RoboAG/projekt_gluecksrad/Bilder/Entwicklung/2018_02_17_grobe_Platinenanordnung.jpg

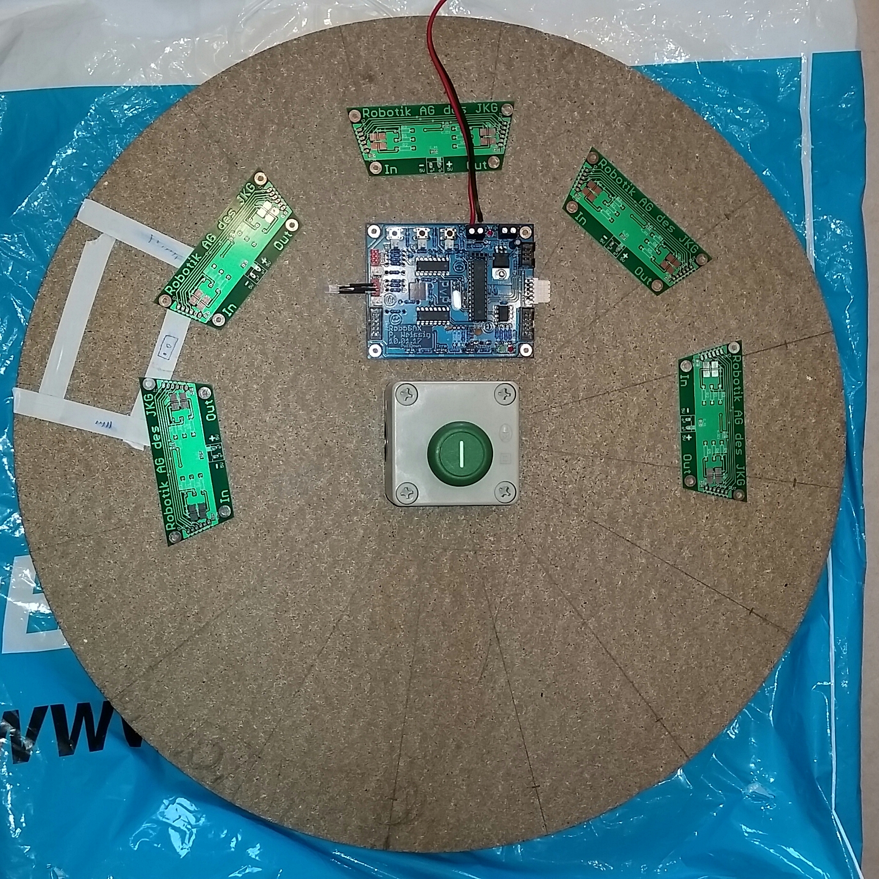
Bilder/Entwicklung/2018_02_17_grobe_Platinenanordnung.jpg
