RoboAG/projekt_gluecksrad/Bilder/Entwicklung/2018_03_07_gluecksrad_zwischenstand.jpg

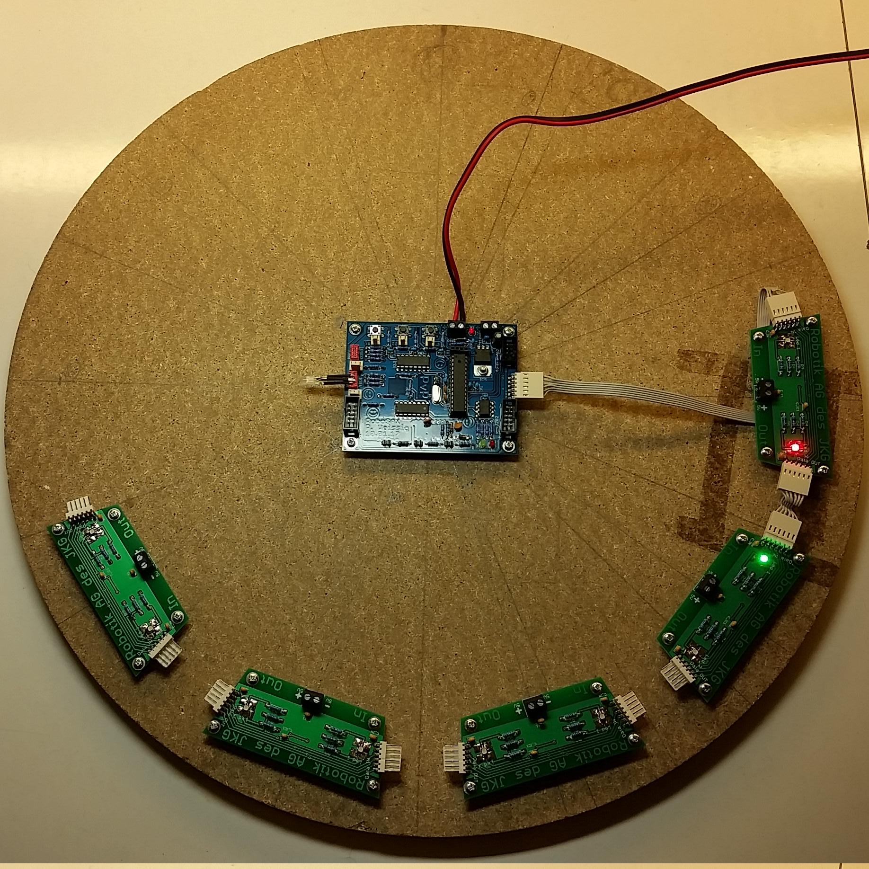
Bilder/Entwicklung/2018_03_07_gluecksrad_zwischenstand.jpg
