RoboAG/projekt_gluecksrad/Bilder/Entwicklung/2018_03_11_stehendes_Stativ.jpg

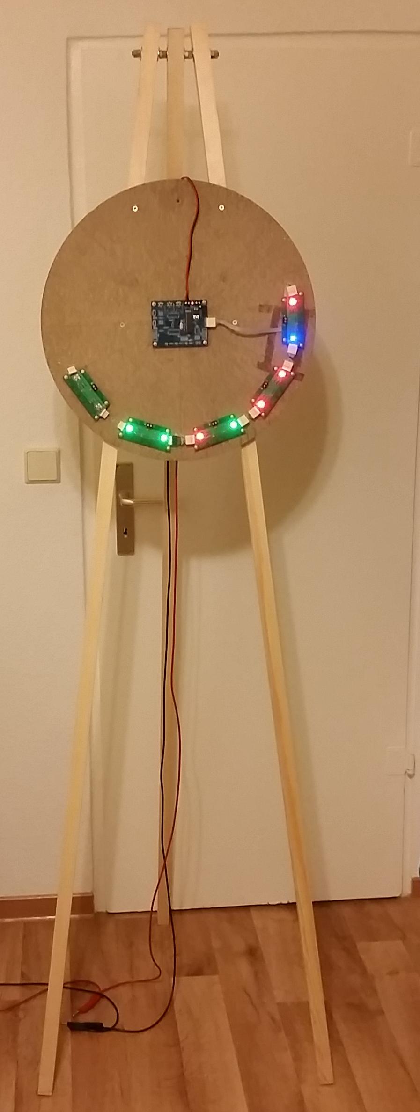
Bilder/Entwicklung/2018_03_11_stehendes_Stativ.jpg
