RoboAG/projekt_gluecksrad/Schaltungen/LED-Platine/2017_06_25_tim/circuit.png

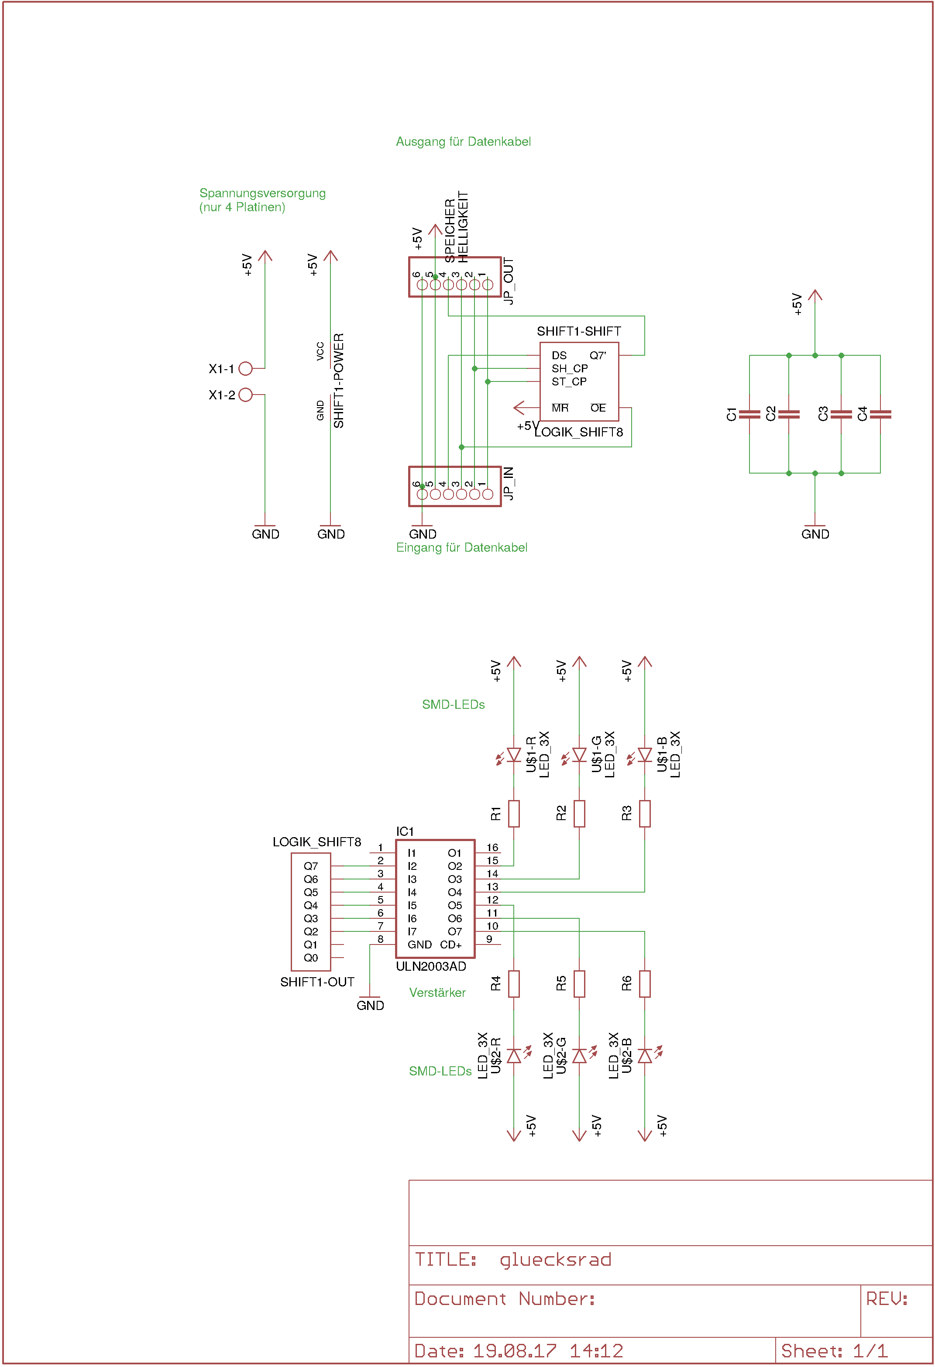
Schaltungen/LED-Platine/2017_06_25_tim/circuit.png
