RoboAG/projekt_gluecksrad/Schaltungen/LED-Platine/2017_06_25_tim/parts_bottom.png

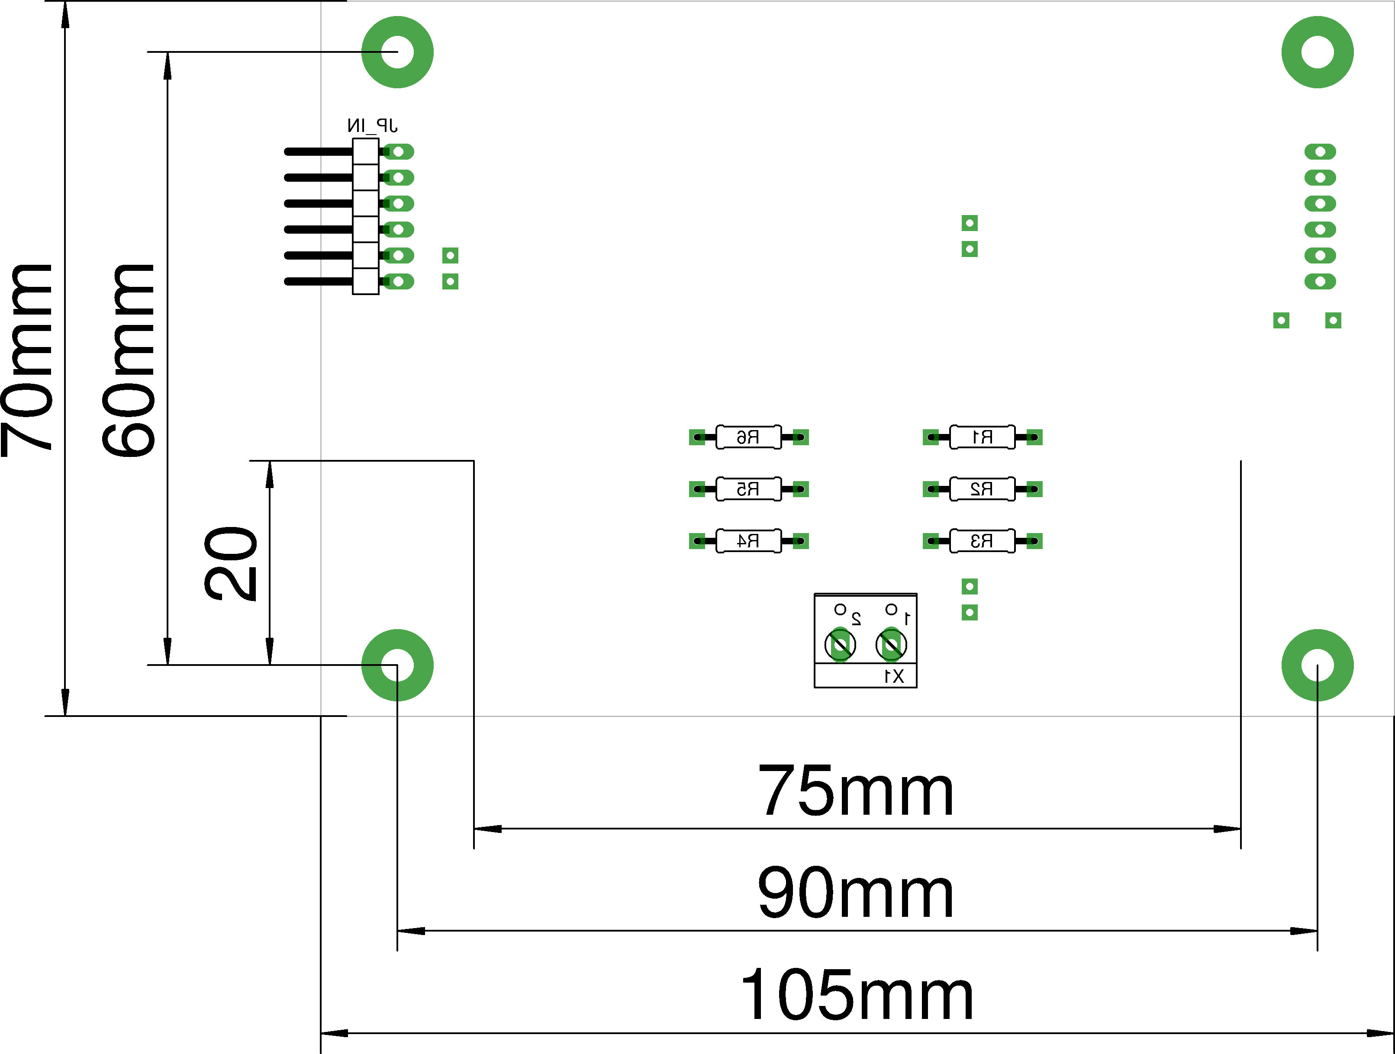
Schaltungen/LED-Platine/2017_06_25_tim/parts_bottom.png
