RoboAG/projekt_gluecksrad/Schaltungen/LED-Platine/2018_01_31_neu/export/images/parts_bottom.png

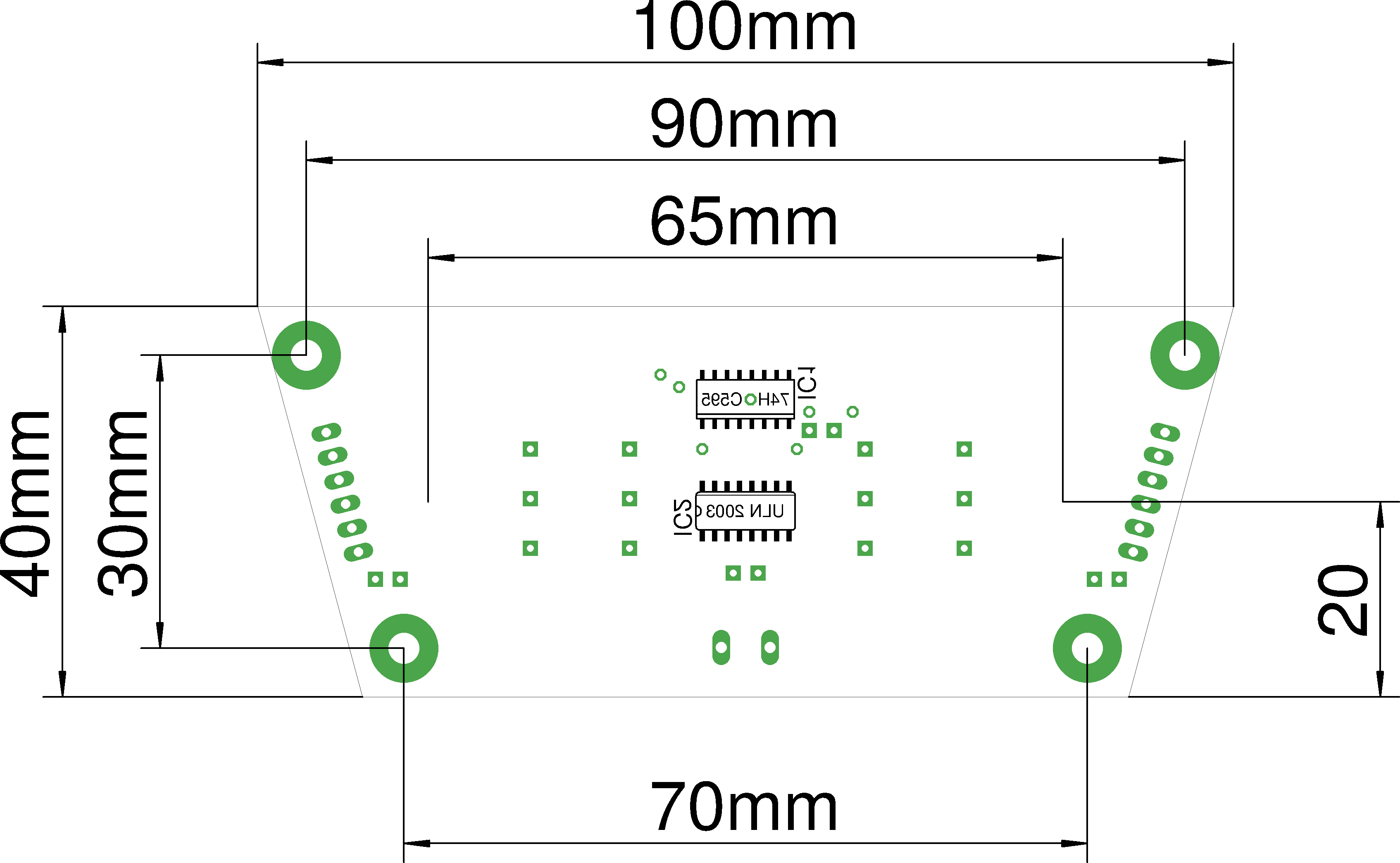
Schaltungen/LED-Platine/2018_01_31_neu/export/images/parts_bottom.png
