RoboAG/projekt_gluecksrad/Schaltungen/LED-Platine/2018_01_31_neu/export/images/parts_top.png

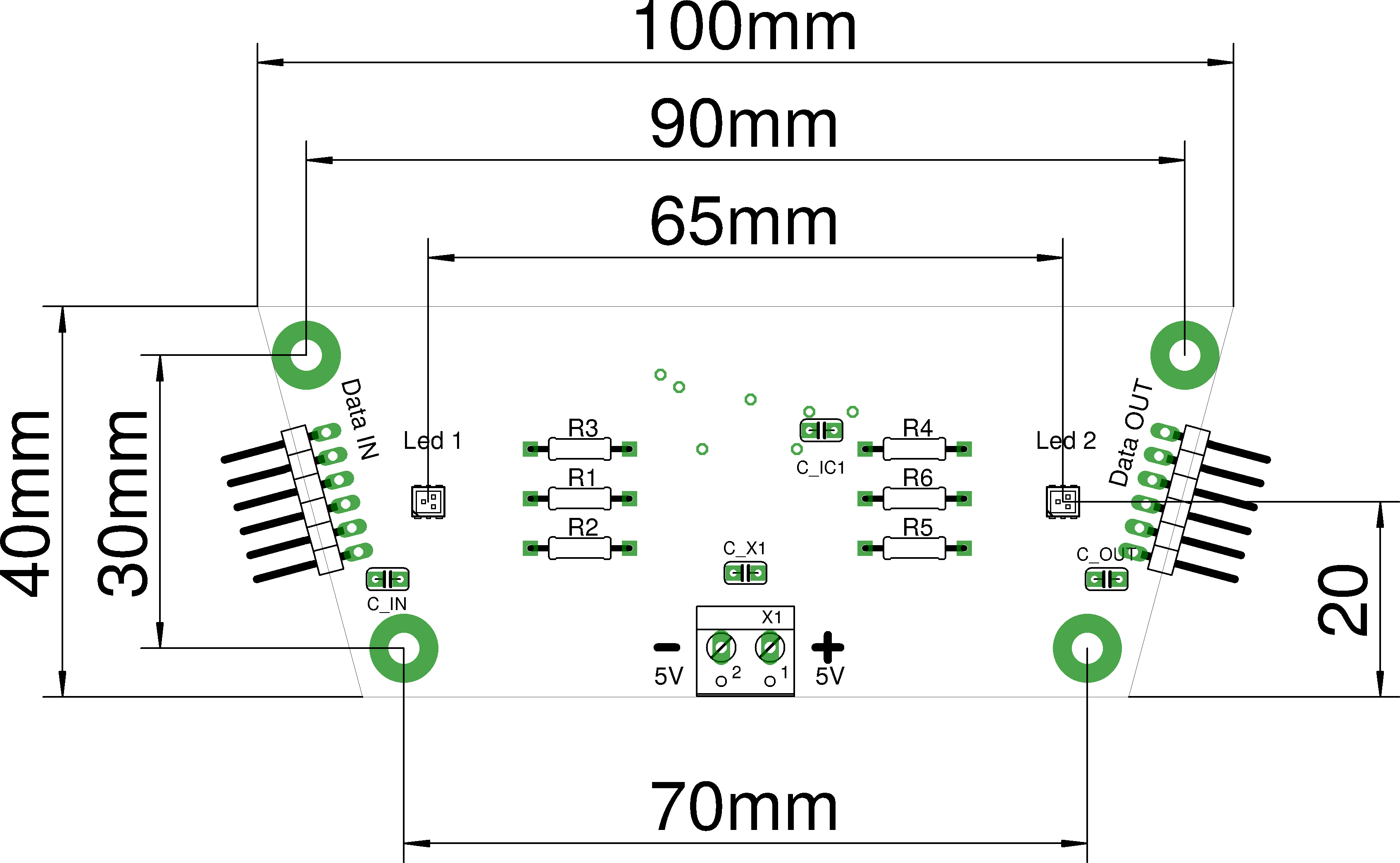
Schaltungen/LED-Platine/2018_01_31_neu/export/images/parts_top.png
