RoboAG/projekt_gluecksrad/Schaltungen/Steuerungsplatine/export/images/parts_roboag.png

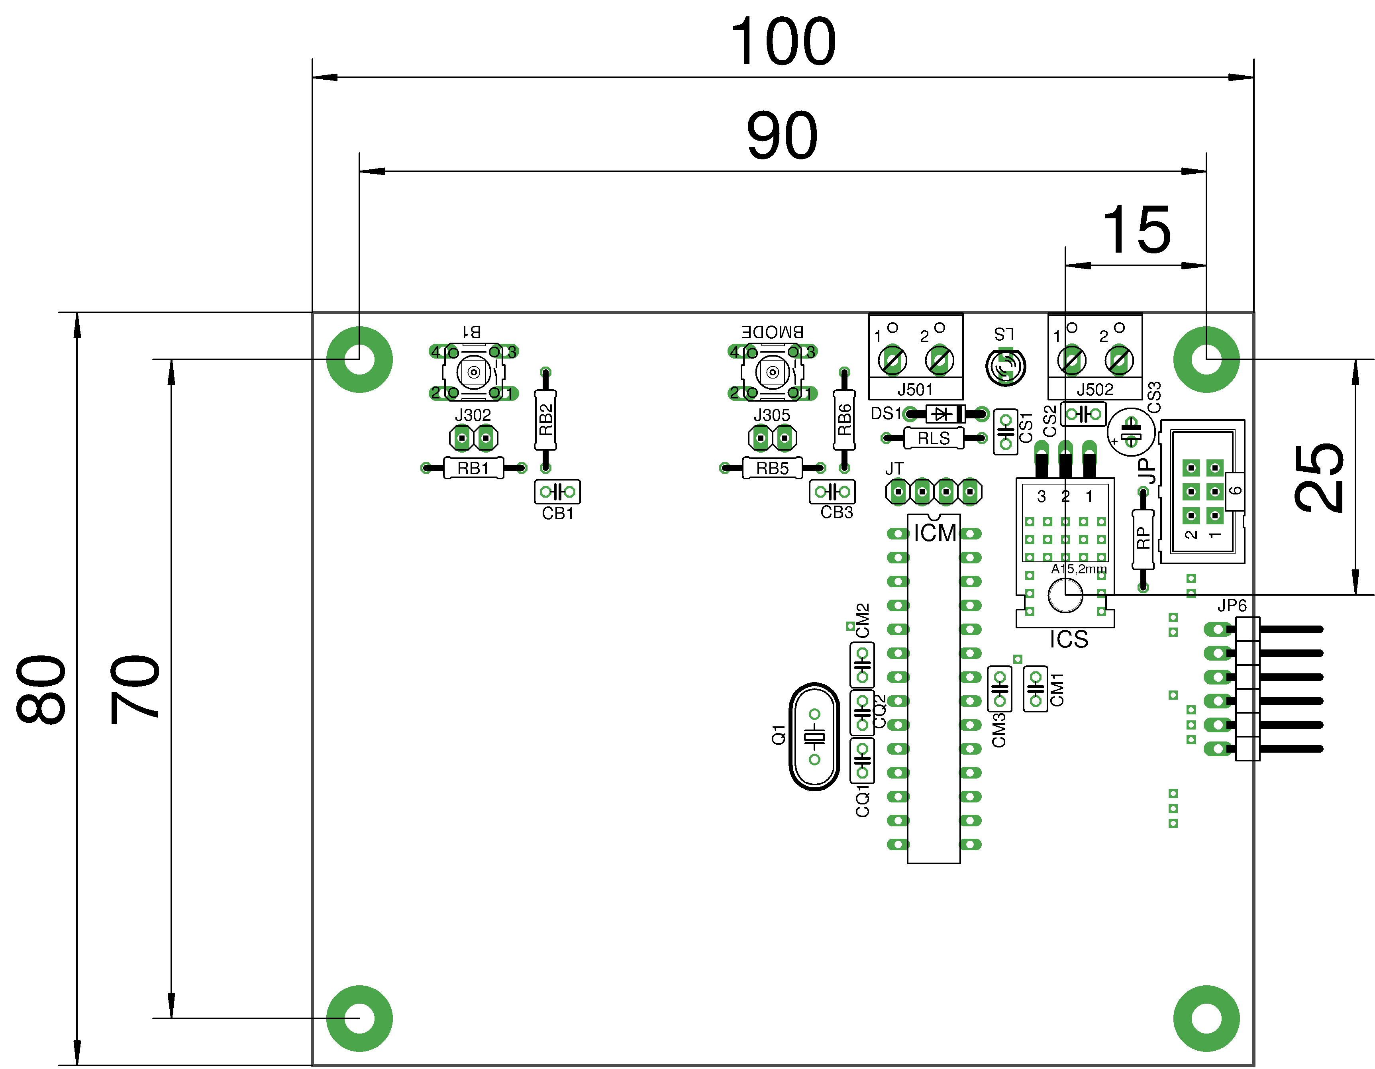
Schaltungen/Steuerungsplatine/export/images/parts_roboag.png
